MohamedBenomar/EPS-NanoSatLab/Hardware/EPS_v3_Library/3D/DO-214BA_VIS.step

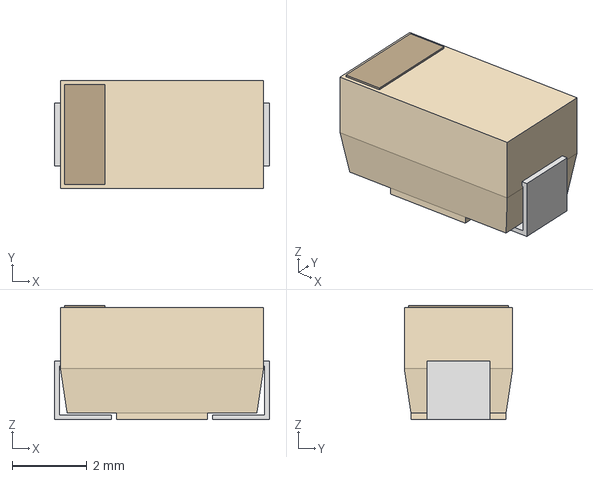
[picture p20: CAD file, 2024-02-26]
Hardware/EPS_v3_Library/3D/DO-214BA_VIS.step
5.74 x 2.90 x 3.05 mm
