MohamedBenomar/EPS-NanoSatLab/Hardware/EPS_v3_Library/3D/DMN1019USN-7_SOT_9USN-7_DIO.step

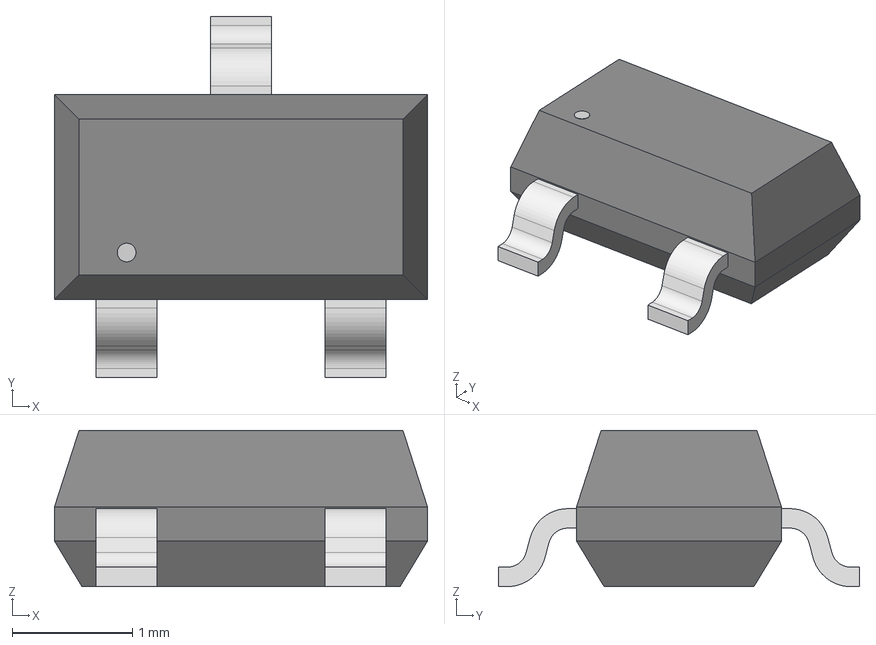
[picture p21: CAD file, 2024-02-26]
Hardware/EPS_v3_Library/3D/DMN1019USN-7_SOT_9USN-7_DIO.step
3.10 x 3.00 x 1.30 mm
