MohamedBenomar/EPS-NanoSatLab/Hardware/EPS_v3_Library/3D/IND_TAIYO_NR10050_TAY.step

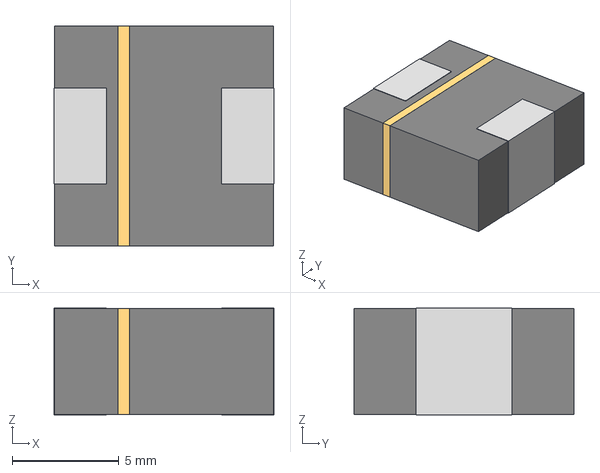
[picture p22: CAD file, 2024-02-26]
Hardware/EPS_v3_Library/3D/IND_TAIYO_NR10050_TAY.step
10.3 x 10.3 x 5.00 mm
