MohamedBenomar/EPS-NanoSatLab/Hardware/EPS_v3_Library/3D/IND_CB_DRA125.step

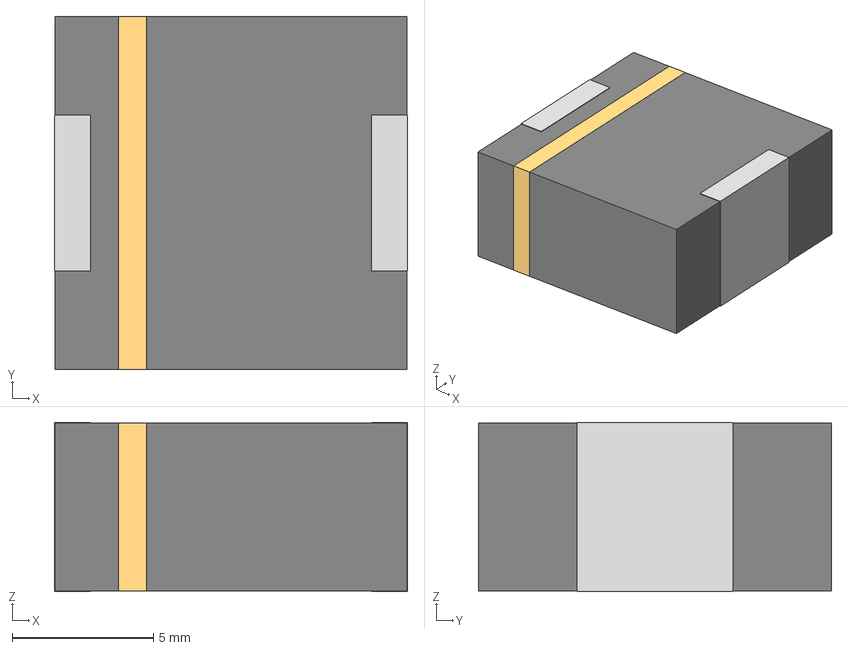
[picture p23: CAD file, 2024-02-26]
Hardware/EPS_v3_Library/3D/IND_CB_DRA125.step
12.5 x 12.5 x 5.99 mm
